thedarknet/defcon25-badge/software/firmware/src/badge/MessageState.h

#ifndef EVENT_STATE_H
#define EVENT_STATE_H

#include "menus.h"
#include "Radio/RFM69.h"

class MessageState: public StateBase {
public:
	struct RadioMessage {
		char Msg[RF69_MAX_DATA_LEN];
		uint16_t FromUID;
		int8_t Rssi;
		RadioMessage();
	};
	enum {
		MESSAGE_LIST, DETAIL
	};
public:
	MessageState();
	virtual ~MessageState();
	void addRadioMessage(const char *msg, uint16_t msgSize, uint16_t uid, uint8_t rssi);
	bool hasNewMessage() {return NewMessage;}
protected:
	virtual ErrorType onInit(RunContext &rc);
	virtual ReturnStateContext onRun(RunContext &rc);
	virtual ErrorType onShutdown();
private:
	RadioMessage RMsgs[8];
	uint8_t InternalState;
	GUI_ListData RadioList;
	GUI_ListItemData Items[8];
	uint8_t CurrentPos:7;
	uint8_t NewMessage:1;
public:
	static const uint16_t MAX_R_MSGS = (sizeof(RMsgs) / sizeof(RMsgs[0]));
};
/*
class EventState: public StateBase {
public:
	struct MessageData {
		char Msg[24];
		MessageData();
	};
public:
	EventState();
	virtual ~EventState();
	void addMessage(const char *pMsg);
protected:
	virtual ErrorType onInit();
	virtual ReturnStateContext onRun(QKeyboard &kb);
	virtual ErrorType onShutdown();
private:
	MessageData Msgs[5];
	uint8_t CurrentPos;
	GUI_ListData EventList;
	GUI_ListItemData Items[5];
};
*/
#endif
