thedarknet/defcon25-badge/software/firmware/src/badge/SendMsgState.h

#ifndef SEND_MSG_STATE_H
#define SEND_MSG_STATE_H

#include "menus.h"

class SendMsgState: public StateBase {
public:
	static const uint16_t NO_CONTACT = 0xFFFF;
	enum INTERNAL_STATE {
		TYPE_MESSAGE, CONFIRM_SEND, SENDING
	};
	SendMsgState();
	virtual ~SendMsgState();
	void setContactToMessage(const uint16_t radioID, const char *agentName);
protected:
	virtual ErrorType onInit(RunContext &rc);
	virtual ReturnStateContext onRun(RunContext &rc);
	virtual ErrorType onShutdown();
private:
	uint16_t RadioID;
	const char *AgentName;
	char MsgBuffer[60];
	INTERNAL_STATE InternalState;

};


#endif
