thedarknet/defcon25-badge/software/firmware/src/badge/Radio/RFM69.h

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
// Licence can be viewed at                               
// http://www.gnu.org/licenses/gpl-3.0.txt
//
// Please maintain this license information along with authorship
// and copyright notices in any redistribution of this code
// **********************************************************************************
#ifndef RFM69_h
#define RFM69_h
#include <stm32f3xx.h>

#define DONT_USE_ACK

#define RF69_MAX_DATA_LEN       61 // to take advantage of the built in AES/CRC we want to limit the frame size to the internal FIFO size (66 bytes - 3 bytes overhead - 2 bytes crc)
//#define RF69_SPI_CS             GPIO_PIN_4 // SS is the SPI slave select pin, for instance D10 on ATmega328

// INT0 on AVRs should be connected to RFM69's DIO0 (ex on ATmega328 it's D2, on ATmega644/1284 it's D2)
#if defined(__AVR_ATmega168__) || defined(__AVR_ATmega328P__) || defined(__AVR_ATmega88) || defined(__AVR_ATmega8__) || defined(__AVR_ATmega88__)
  #define RF69_IRQ_PIN          2
  #define RF69_IRQ_NUM          0
#elif defined(__AVR_ATmega644P__) || defined(__AVR_ATmega1284P__)
  #define RF69_IRQ_PIN          2
  #define RF69_IRQ_NUM          2
#elif defined(__AVR_ATmega32U4__)
  #define RF69_IRQ_PIN          3
  #define RF69_IRQ_NUM          0
#elif defined(__arm__)//Use pin 10 or any pin you want
  #define RF69_IRQ_PIN          10
  #define RF69_IRQ_NUM          10
#else 
  #define RF69_IRQ_PIN          GPIO_PIN_0
  #define RF69_IRQ_NUM          0  
#endif


#define CSMA_LIMIT              -45 // upper RX signal sensitivity threshold in dBm for carrier sense access
#define RF69_MODE_SLEEP         0 // XTAL OFF
#define RF69_MODE_STANDBY       1 // XTAL ON
#define RF69_MODE_SYNTH         2 // PLL ON
#define RF69_MODE_RX            3 // RX MODE
#define RF69_MODE_TX            4 // TX MODE

// available frequency bands
#define RF69_315MHZ            31 // non trivial values to avoid misconfiguration
#define RF69_433MHZ            43
#define RF69_868MHZ            86
#define RF69_915MHZ            91

#define null                  0
#define COURSE_TEMP_COEF    -90 // puts the temperature reading in the ballpark, user can fine tune the returned value
//#define RF69_BROADCAST_ADDR 255
#define RF69_BROADCAST_ADDR 0xFFFF
#define RF69_CSMA_LIMIT_MS 1000
#define RF69_TX_LIMIT_MS   1000
#define RF69_FSTEP  61.03515625 // == FXOSC / 2^19 = 32MHz / 2^19 (p13 in datasheet)

// TWS: define CTLbyte bits
#define RFM69_CTL_SENDACK   0x80
#define RFM69_CTL_REQACK    0x40



class RFM69 {
  public:
	typedef uint16_t RadioAddrType;
    static volatile uint8_t DATA[RF69_MAX_DATA_LEN]; // recv/xmit buf, including header & crc bytes
    static volatile uint8_t DATALEN;
    static volatile RadioAddrType SENDERID;
    static volatile RadioAddrType TARGETID; // should match _address
    static volatile uint8_t PAYLOADLEN;
    static volatile uint8_t ACK_REQUESTED;
    static volatile uint8_t ACK_RECEIVED; // should be polled immediately after sending a packet with ACK request
    static volatile int16_t RSSI; // most accurate RSSI during reception (closest to the reception)
    static volatile uint8_t _mode; // should be protected?

    RFM69(uint8_t slaveSelectPin=15, uint8_t interruptPin=RF69_IRQ_PIN, bool isRFM69HW=false, uint8_t interruptNum=RF69_IRQ_NUM);

    bool initialize(uint8_t freqBand, RadioAddrType ID, uint8_t networkID=1);
    //this is to use the radio's address filtering
    //void setAddress(uint8_t addr);
    void setNetwork(uint8_t networkID);
    bool canSend();
    virtual void send(RadioAddrType toAddress, const void* buffer, uint8_t bufferSize, bool requestACK=false);
    virtual bool sendWithRetry(RadioAddrType toAddress, const void* buffer, uint8_t bufferSize, uint8_t retries=2, uint8_t retryWaitTime=40); // 40ms roundtrip req for 61byte packets
    virtual bool receiveDone();
    uint8_t getCurrentGain();
    uint8_t getImpedenceLevel();
    uint8_t getRSSIThreshHold();
    bool ACKReceived(RadioAddrType fromNodeID);
    bool ACKRequested();
    virtual void sendACK(const void* buffer = "", uint8_t bufferSize=0);
    uint32_t getFrequency();
    void setFrequency(uint32_t freqHz);
    void encrypt(const char* key);
    void setCS(uint8_t newSPISlaveSelect);
    int16_t readRSSI(bool forceTrigger=false);
    void promiscuous(bool onOff=true);
    virtual void setHighPower(bool onOFF=true); // has to be called after initialize() for RFM69HW
    virtual void setPowerLevel(uint8_t level); // reduce/increase transmit power level
    void sleep();
    uint8_t readTemperature(uint8_t calFactor=0); // get CMOS temperature (8bit)
    void rcCalibration(); // calibrate the internal RC oscillator for use in wide temperature variations - see datasheet section [4.3.5. RC Timer Accuracy]

    // allow hacking registers by making these public
    uint8_t readReg(uint8_t addr);
    void writeReg(uint8_t addr, uint8_t val);
#ifdef READ_ALL_REGS
    void readAllRegs();
#endif
    virtual ~RFM69();
  protected:
    static void isr0();
    void virtual interruptHandler();
    static volatile bool _inISR;
    virtual void sendFrame(RadioAddrType toAddress, const void* buffer, uint8_t size, bool requestACK=false, bool sendACK=false);

    static RFM69* selfPointer;
    uint8_t _slaveSelectPin;
    uint8_t _interruptPin;
    uint8_t _interruptNum;
    RadioAddrType _address;
    bool _promiscuousMode;
    uint8_t _powerLevel;
    bool _isRFM69HW;


    virtual void receiveBegin();
    virtual void setMode(uint8_t mode);
    virtual void setHighPowerRegs(bool onOff);
    virtual void select();
    virtual void unselect();
    inline void maybeInterrupts();
};

#endif
