thedarknet/defcon25-badge/software/firmware/src/badge/GameOfLife.cpp

#include "GameOfLife.h"
#include "leddc25.h"
#include <stdlib.h>

GameOfLife::GameOfLife() :
		Generations(0), CurrentGeneration(0), Neighborhood(0), InternalState(GameOfLife::GAME), DisplayMessageUntil(0) {
}

GameOfLife::~GameOfLife() {

}

//static uint8_t TIMES_SCREEN_SAVER=3; //due to lack of code space to put in configurable sleep time

ErrorType GameOfLife::onInit(RunContext &rc) {
	UNUSED(rc);
	InternalState = INIT;
	return ErrorType();
}

bool GameOfLife::shouldDisplayMessage() {
	return HAL_GetTick() < DisplayMessageUntil;
}

static uint8_t noChange = 0;

ReturnStateContext GameOfLife::onRun(RunContext &rc) {
	switch (InternalState) {
	case INIT: {
		rc.getDisplay().fillScreen(RGBColor::BLACK);
		DisplayMessageUntil = HAL_GetTick() + 3000;
		initGame();
		int danceType = rand()%LedDC25::TOTAL_DANCE_TYPES;
		rc.getLedControl().setDanceType(LedDC25::LED_DANCE_TYPE(danceType));
		noChange = 0;
	}
		break;
	case MESSAGE:
		rc.getDisplay().drawString(0, 10, &UtilityBuf[0], RGBColor::BLACK, RGBColor::WHITE, 1, true);
		InternalState = TIME_WAIT;
		break;
	case TIME_WAIT:
		if (!shouldDisplayMessage()) {
			InternalState = GAME;
			rc.getDisplay().fillScreen(RGBColor::BLACK);
		}
		break;
	case GAME: {
		if (CurrentGeneration >= Generations) {
			InternalState = INIT;
		} else {
			uint16_t count = 0;
			//uint8_t bitToCheck = CurrentGeneration % 32;
			for (uint16_t j = 0; j < height; j++) {
				for (uint16_t k = 0; k < width; k++) {
					if ((gol[j] & (1 << k)) != 0) {
						rc.getDisplay().drawPixel(k * 4, j * 2 + 10, RGBColor::WHITE);
						count++;
					} else {
						rc.getDisplay().drawPixel(k * 4, j * 2 + 10, RGBColor::BLACK);
					}
				}
				rc.checkRadio(HAL_GetTick());
			}
			if (0 == count) {
				sprintf(&UtilityBuf[0], "   ALL DEAD\n   After %d\n   generations", CurrentGeneration);
				CurrentGeneration = Generations + 1;
				InternalState = MESSAGE;
				DisplayMessageUntil = HAL_GetTick() + 3000;
				rc.getDisplay().fillScreen(RGBColor::BLACK);
			} else {
				uint32_t tmp[sizeof(gol)];
				if (!life(&gol[0], Neighborhood, width, height, &tmp[0])) {
					noChange++;
					if (noChange > 6) {
						CurrentGeneration = Generations + 1;
					}
				}
			}
			CurrentGeneration++;
		}
	}
		break;
	case SLEEP:
		break;
	}
	if (rc.getKB().getLastKeyReleased() == QKeyboard::NO_PIN_SELECTED) {
		return ReturnStateContext(this);
	} else {
		rc.getLedControl().setDanceType(LedDC25::NONE);
		return ReturnStateContext(StateFactory::getMenuState());
	}
}

ErrorType GameOfLife::onShutdown() {
	return ErrorType();
}

void GameOfLife::initGame() {
	uint32_t start = HAL_GetTick();
	CurrentGeneration = 0;
	Neighborhood = (start & 1) == 0 ? 'm' : 'v';
	srand(start);
	short chanceToBeAlive = rand() % 50;
	memset(&gol[0], 0, sizeof(gol));
	for (int j = 0; j < height ; j++) {
		for (int i = 0; i < width; i++) {
			if ((rand() % 100) < chanceToBeAlive) {
				gol[j] |= (1 << i);
			}
		}
	}
	Generations = 100 + (rand() % 75);
	InternalState = MESSAGE;
	DisplayMessageUntil = start + 3000;
	sprintf(&UtilityBuf[0], "  Max\n  Generations: %d", Generations);
}
//The life function is the most important function in the program.
//It counts the number of cells surrounding the center cell, and
//determines whether it lives, dies, or stays the same.
bool GameOfLife::life(uint32_t *array, char choice, short width, short height, uint32_t *temp) {
	//Copies the main array to a temp array so changes can be entered into a grid
	//without effecting the other cells and the calculations being performed on them.
	memcpy(&temp[0], &array[0], sizeof(gol));
	for (int j = 1; j < height - 1; ++j) {
		for (int i = 0; i < width; ++i) {
			if (choice == 'm') {
				//The Moore neighborhood checks all 8 cells surrounding the current cell in the array.
				int count = 0;
				count = ((array[j - 1] & (1 << i)) > 0 ? 1 : 0) + ((array[j - 1] & (1 << (i - 1))) > 0 ? 1 : 0)
						+ ((array[j] & (1 << (i - 1))) > 0 ? 1 : 0) + ((array[j + 1] & (1 << (i - 1))) > 0 ? 1 : 0)
						+ ((array[j + 1] & (1 << i)) > 0 ? 1 : 0) + ((array[j + 1] & (1 << (i + 1))) > 0 ? 1 : 0)
						+ ((array[j] & (1 << (i + 1))) > 0 ? 1 : 0) + ((array[j - 1] & (1 << (i + 1))) > 0 ? 1 : 0);
				if (count < 2 || count > 3)
					temp[j] &= ~(1 << i);
				if (count == 3)
					temp[j] |= (1 << i);
			} else if (choice == 'v') {
				//The Von Neumann neighborhood checks only the 4 surrounding cells in the array, (N, S, E, and W).
				int count = 0;
				count = ((array[j - 1] & (1 << i)) > 0 ? 1 : 0) + ((array[j] & (1 << (i - 1))) > 0 ? 1 : 0)
						+ ((array[j + 1] & (1 << i)) > 0 ? 1 : 0) + ((array[j] & (1 << (i + 1))) > 0 ? 1 : 0);
				//The cell dies.
				if (count < 2 || count > 3)
					temp[j] &= ~(1 << i);
				//The cell either stays alive, or is "born".
				if (count == 3)
					temp[j] |= (1 << i);
			}
		}
	}
	if (memcmp(&array[0], &temp[0], sizeof(gol)) == 0) {
		return false;
	} else {
		//Copies the completed temp array back to the main array.
		memcpy(&array[0], &temp[0], sizeof(gol));
		return true;
	}
}
