thedarknet/defcon25-badge/software/firmware/src/badge/3d/renderer.h

#ifndef RENDERER_H
#define RENDERER_H

#include "vec_math.h"
#include "../display_device.h"


extern Matrix ModelView;
extern Matrix Viewport;
extern Matrix Projection;

struct VertexStruct {
	Vec3f pos;
	RGBColor color;
	//VertexStruct(const Vec3f &p, const RGBColor &r) : pos(p), color(r) {}
};


class Model {
	//no model matrix to save space and computation we assume identity
public:
	enum MODEL_FORMAT {
		VERTS,
		STRIPS
	};
	Model();
	void set(const VertexStruct *v, uint16_t nv, const uint16_t *i, uint16_t ni, MODEL_FORMAT format);
	const Vec3f &normal(uint16_t face, uint8_t nVert) const;
	const Vec3f &vert(uint16_t face, uint8_t nVert) const;
	uint32_t nFaces() const;
	const Matrix &getModelTransform() const {return ModelTransform;}
	void setTransformation(float t) {ModelTransform.setRotation(t);}
	void scale(float t) {ModelTransform.scale(t);}
private:
	const VertexStruct *Verts;
	uint16_t NumVerts;
	const uint16_t *Indexes;
	uint8_t NumIndexes;
	Matrix ModelTransform;
	MODEL_FORMAT Format;
};


class IShader {
public:
	IShader();
	virtual ~IShader() = 0;
	virtual Vec3i vertex(const Matrix &ModelViewProj, const Model &model, int iface, int nthvert) = 0;
	virtual bool fragment(Vec3f bar, RGBColor &color) = 0;
	void setLightDir(const Vec3f &ld);
	const Vec3f &getLightDir() const;
private:
	Vec3f LightDir;
};

class FlatShader: public IShader {
public:
	FlatShader();
	virtual ~FlatShader();

	virtual Vec3i vertex(const Matrix &ModelViewProj, const Model &model, int iface, int nthvert);
	virtual bool fragment(Vec3f bar, RGBColor &color);
private:
	mat<3, 3, float> varying_tri;
};

struct GouraudShader: public IShader {
public:
	GouraudShader();
	virtual ~GouraudShader();
	virtual Vec3i vertex(const Matrix &ModelViewProj, const Model &model, int iface, int nthvert);
	virtual bool fragment(Vec3f bar, RGBColor &color);
private:
	mat<3, 3, float> varying_tri;
	Vec3f varying_ity;
};

class ToonShader: public IShader {
public:
	ToonShader();
	virtual ~ToonShader();
	virtual Vec3i vertex(const Matrix &ModelViewProj, const Model &model, int iface, int nthvert);
	virtual bool fragment(Vec3f bar, RGBColor &color);
private:
	mat<3, 3, float> varying_tri;
	Vec3f varying_ity;

};

void viewport(int x, int y, int w, int h);
void projection(float coeff = 0.f); // coeff = -1/c
void lookat(const Vec3f &eye, const Vec3f &center, const Vec3f &up);
//void triangle(Vec3i *pts, IShader &shader, BitArray &zbuffer, DisplayST7735 *display);
void triangle(Vec3i *pts, IShader &shader, BitArray &zbuffer, DisplayST7735 *display, const Vec2i &bboxmin, const Vec2i &bboxmax, uint16_t canvasWdith);

template<typename T> T CLAMP(const T& value, const T& low, const T& high) {
	return value < low ? low : (value > high ? high : value);
}

#endif
