thedarknet/defcon25-badge/software/firmware/src/badge/3d/menu3d.h

#ifndef MENU3D
#define MENU3D

#include "../menus.h"
#include "renderer.h"

class Model;

class Menu3D : public StateBase {
public:
	Menu3D();
	virtual ~Menu3D();
public:
protected:
	virtual ErrorType onInit(RunContext &rc);
	virtual ReturnStateContext onRun(RunContext &rc);
	virtual ErrorType onShutdown();
	void initMenu3d(RunContext &rc);
	void update(RunContext &rc);
	void render(RunContext &rc);
private:
	Model model;
	Vec3f light_dir;
	Vec3f eye;
	static const Vec3f center;
	static const Vec3f up;
	uint8_t CanvasWidth;
	uint8_t CanvasHeight;
};

#endif
