thedarknet/defcon25-badge/software/firmware/src/badge/bitarray.h

#ifndef BIT_ARRAY_H
#define BIT_ARRAY_H

#include <stdint.h>

class BitArray {
public:
	BitArray(uint8_t *array, uint32_t slots, uint8_t bitsPerSlot);
	void clear();
	uint8_t getValueAsByte(uint32_t slot);
	void setValueAsByte(uint32_t slot, uint8_t value);
	uint8_t getBitsPerSlot() {return BitsPerSlot;}
private:
	uint8_t *Array;
	const uint32_t Slots;
	const uint8_t BitsPerSlot;
	const uint32_t NumBytes;
};

#endif
