thedarknet/defcon25-badge/software/firmware/src/badge/crc.h

/**
 * \file crc.h
 * Functions and types for CRC checks.
 *
 * Generated on Mon Jul 18 07:08:22 2016,
 * by pycrc v0.9, https://pycrc.org
 * using the configuration:
 *    Width         = 8
 *    Poly          = 0x07
 *    Xor_In        = 0x00
 *    ReflectIn     = False
 *    Xor_Out       = 0x00
 *    ReflectOut    = False
 *    Algorithm     = table-driven
 *****************************************************************************/
#ifndef __CRC_H__
#define __CRC_H__

#include <stdlib.h>
#include <stdint.h>

#ifdef __cplusplus
extern "C" {
#endif


/**
 * The definition of the used algorithm.
 *
 * This is not used anywhere in the generated code, but it may be used by the
 * application code to call algoritm-specific code, is desired.
 *****************************************************************************/
#define CRC_ALGO_TABLE_DRIVEN 1


/**
 * The type of the CRC values.
 *
 * This type must be big enough to contain at least 8 bits.
 *****************************************************************************/
typedef uint_fast8_t crc_t;


/**
 * Calculate the initial crc value.
 *
 * \return     The initial crc value.
 *****************************************************************************/
static inline crc_t crc_init(void)
{
    return 0x00;
}


/**
 * Update the crc value with new data.
 *
 * \param crc      The current crc value.
 * \param data     Pointer to a buffer of \a data_len bytes.
 * \param data_len Number of bytes in the \a data buffer.
 * \return         The updated crc value.
 *****************************************************************************/
crc_t crc_update(crc_t crc, const void *data, size_t data_len);


/**
 * Calculate the final crc value.
 *
 * \param crc  The current crc value.
 * \return     The final crc value.
 *****************************************************************************/
static inline crc_t crc_finalize(crc_t crc)
{
    return crc ^ 0x00;
}


#ifdef __cplusplus
}           /* closing brace for extern "C" */
#endif

#endif      /* __CRC_H__ */
